oficinadesonido/hanan-cumbia/hananMiniPcb/BD1.kicad_sch

## KiCad design hananMiniPcb/BD1.kicad_sch (2026-06-10)

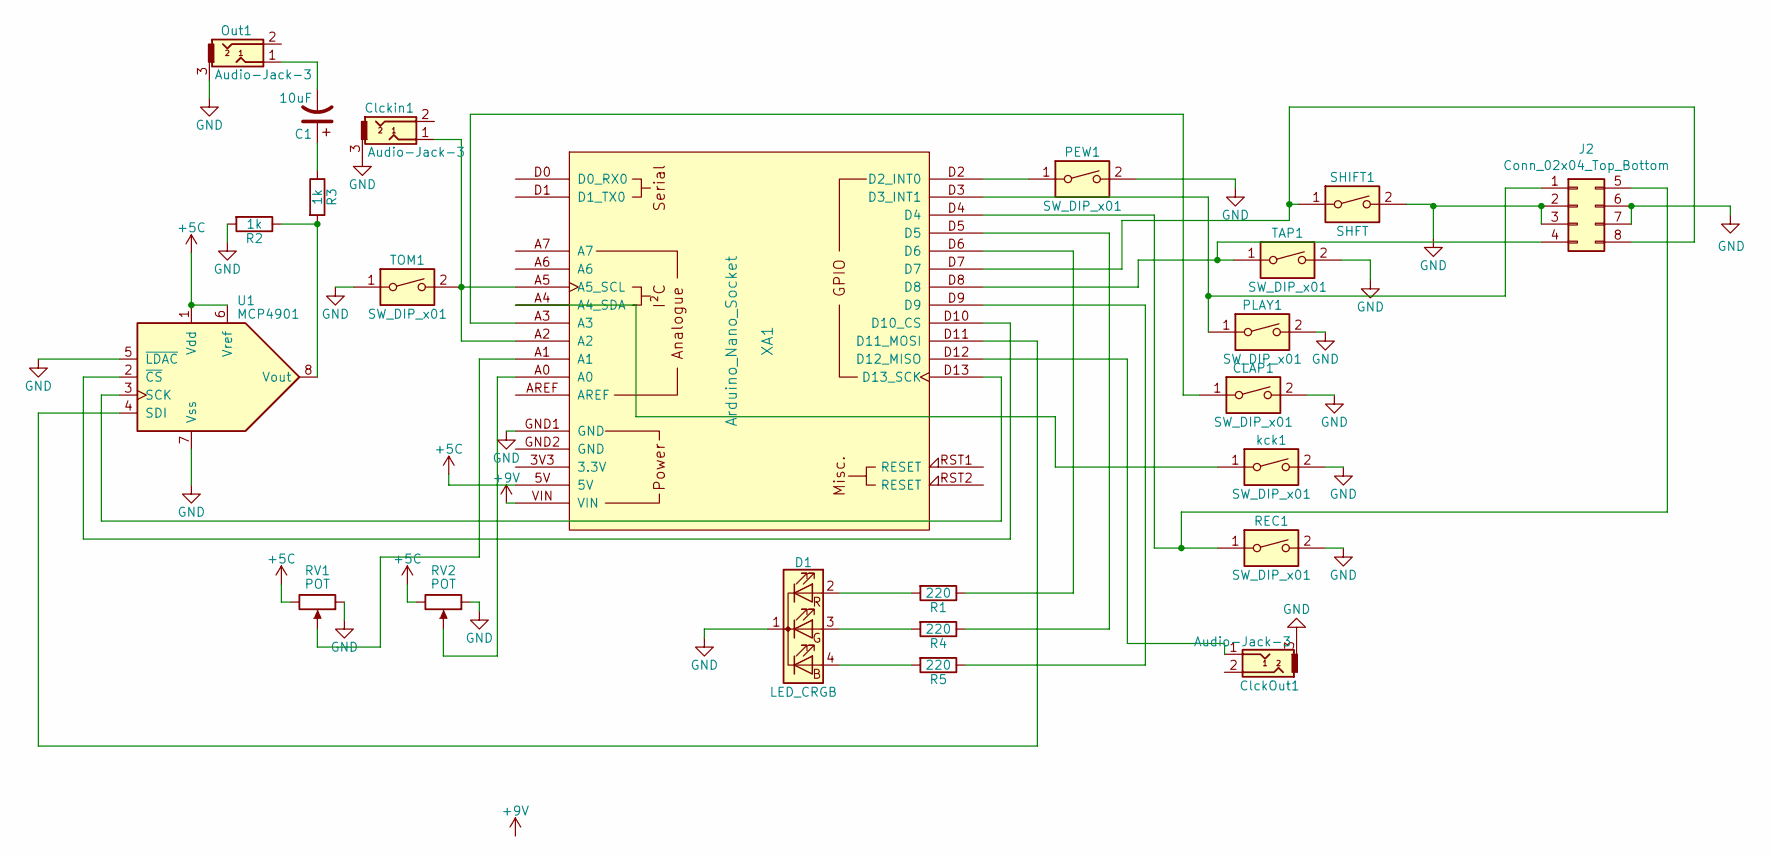
[picture p6: schematic BD1.kicad_sch]

Parts:
C1: 10uF; CP_Radial_D4.0mm_P2.00mm
CLAP1: SW_DIP_x01; SW_PUSH-12mm
ClckOut1: Audio-Jack-3; CONN_Jack_Female_3.5mm_THD
Clckin1: Audio-Jack-3; CONN_Jack_Female_3.5mm_THD
D1: LED_CRGB; LED_RGB_CATCOM_sep
J2: Conn_02x04_Top_Bottom; PinHeader_1x08_P2.00mm_Vertical
Out1: Audio-Jack-3; CONN_Jack_Female_3.5mm_THD
PEW1: SW_DIP_x01; SW_PUSH-12mm
PLAY1: SW_DIP_x01; SW_PUSH_6mm
R1, R4, R5: 220; R_Axial_DIN0207_L6.3mm_D2.5mm_P7.62mm_Horizontal
R2, R3: 1k; R_Axial_DIN0207_L6.3mm_D2.5mm_P7.62mm_Horizontal
REC1: SW_DIP_x01; SW_PUSH_6mm
RV1, RV2: POT; Potentiometer_Alps_RK09K_Single_Vertical
SHIFT1: SHFT; SW_PUSH_6mm
TAP1: SW_DIP_x01; SW_PUSH_6mm
TOM1: SW_DIP_x01; SW_PUSH-12mm
U1: MCP4901; DIP-8_W7.62mm_Socket_LongPads
XA1: Arduino_Nano_Socket
kck1: SW_DIP_x01; SW_PUSH-12mm

Connections:
+5C: RV1.3, RV2.3, U1.1 (Vdd), U1.6 (Vref), XA1.5V
+9V: XA1.VIN
GND: CLAP1.2, ClckOut1.3, Clckin1.3, D1.1 (K), J2.2, J2.3, J2.6, J2.7, Out1.3, PEW1.2, PLAY1.2, R2.2, REC1.2, RV1.1, RV2.1, SHIFT1.2, TAP1.2, TOM1.1, U1.5 (~LDAC), U1.7 (Vss), XA1.GND1 (GND), kck1.2
unnamed: C1.1, R3.1
unnamed: C1.2, Out1.1
unnamed: CLAP1.1, XA1.A3
unnamed: ClckOut1.1, XA1.D12 (D12_MISO)
unnamed: Clckin1.1, TOM1.2, XA1.A2, XA1.A5 (A5_SCL)
unnamed: D1.2 (RA), R1.2
unnamed: D1.3 (GA), R4.2
unnamed: D1.4 (BA), R5.2
unnamed: J2.1, PLAY1.1, XA1.D3 (D3_INT1)
unnamed: J2.4, TAP1.1, XA1.D8
unnamed: J2.5, REC1.1, XA1.D4
unnamed: J2.8, SHIFT1.1, XA1.D7
unnamed: PEW1.1, XA1.D2 (D2_INT0)
unnamed: R1.1, XA1.D6
unnamed: R2.1, R3.2, U1.8 (Vout)
unnamed: R4.1, XA1.D5
unnamed: R5.1, XA1.D9
unnamed: RV1.2, XA1.A1
unnamed: RV2.2, XA1.A0
unnamed: U1.2 (~CS), XA1.D10 (D10_CS)
unnamed: U1.3 (SCK), XA1.D13 (D13_SCK)
unnamed: U1.4 (SDI), XA1.D11 (D11_MOSI)
unnamed: XA1.A4 (A4_SDA), kck1.1
