oficinadesonido/hanan-cumbia/firmware/hanan26Taller/DDS.ino

ISR(TIMER2_COMPA_vect) {
  OCR2A = 50;

  // Reloj de tempo estable: avanza siempre, sin importar la carga de CPU.
  audioclock += AUDIOCLOCK_STEP;


    if (playmode==0){ //reverse
  snare_sample = (pgm_read_byte(&samplebank[snare_off+(indexr)]))-127;
  kick_sample = (pgm_read_byte(&samplebank[kick_off+(index2r)]))-127;
  hat_sample = (pgm_read_byte(&samplebank[hat_off+(index3r)]))-127;
  bass_sample = (((pgm_read_byte(&samplebank[bass_off+(index4r)]))))-127;

  B1_freq_sample = pgm_read_byte(&samplebank[hat_off+(index2vr)])-127;
  B2_freq_sample = (pgm_read_byte(&samplebank[bass_off+(index4vr)]))-127;
    }
    
if (playmode==1){
  snare_sample = (pgm_read_byte(&samplebank[snare_off+(index3)]))-127;
  kick_sample = (pgm_read_byte(&samplebank[kick_off+(index4)]))-127;
  hat_sample = (pgm_read_byte(&samplebank[hat_off+(index)]))-127;
  bass_sample = (((pgm_read_byte(&samplebank[bass_off+(index2)]))))-127;
  
  noise_sample = (((pgm_read_byte(&noise_table[(index5)]))))-127;

  B1_freq_sample = pgm_read_byte(&samplebank[hat_off+(index_freq_1)])-127;
  B2_freq_sample = (pgm_read_byte(&samplebank[bass_off+(index_freq_2)]))-127;
}
sample_sum=snare_sample+kick_sample+hat_sample+bass_sample+B1_freq_sample+B2_freq_sample;

if (noise_mode==1){

sample_holder1= (sample_sum^(noise_sample>>1))+127;


if (B1_latch ==0 && B2_latch==0  && B3_latch==0  && B4_latch==0 ){
 sample=127 ;
  }
  else{
sample=sample_holder1;
  }
  
}

if (noise_mode==0){
  sample= ((snare_sample+kick_sample+hat_sample+bass_sample+B1_freq_sample+B2_freq_sample))+127;

}
  byte sample_out=constrain(sample,0,255);


   dac.output(sample_out);

  ///////////////////////////////////////////////////////////////////////////////

  if (playmode==0){
    // length-1: con indice forward en 0 (idle), length a secas leeria [length],
    // fuera del sample (en el bass = fuera del banco -> DC de -127 en reverse).
    indexr=(index3-(snare_length-1))*-1;
    index2r=(index4-(kick_length-1))*-1;
    index3r=(index-(tick_length-1))*-1;
    index4r=(index2-(bass_length-1))*-1;
    index2vr=(index_freq_1-(tick_length-1))*-1;
    index4vr=(index_freq_2-(bass_length-1))*-1;

  }
  
  if (B1_latch==1){
    accumulator += pot1;
    index=(accumulator >> (6));  
    // >= : el indice length ya esta FUERA del sample. En el banco unico, leer
    // [length] del ultimo sample (bass) cae fuera del array -> byte basura (0)
    // -> pico de -127 = clic al final del sonido.
    if (index>=tick_length){

      index=0;
      accumulator=0;
      B1_latch=0;
    }
  }

  if (B2_latch==1){
    accumulator2 += (pot2);
    index2=(accumulator2 >> (6));  
    if (index2>=bass_length){

      index2=0;
      accumulator2=0;
      B2_latch=0;
    }
  }

  if (B3_latch==1){
    accumulator3 += (128);
    index3=(accumulator3 >> 6);  
    if (index3>=snare_length){

      index3=0;
      accumulator3=0;
      B3_latch=0;
    }
  }

  if (B4_latch==1){
    accumulator4 += (157);
   // index4b=(accumulator4 >> (6));  
    index4=(accumulator4 >> (6));
    if (index4>=kick_length){

      index4=0;
      accumulator4=0;
      B4_latch=0;
    }
  }

  accu_freq_1 += kf;
  index_freq_1=(accu_freq_1 >> (6));  
  if (B1_seq_trigger==1){
    kf=B1_freq_sequence[loopstepf+banko];
    kfe=kf;
  }

  if (index_freq_1>=tick_length){
    kf=0;
    index_freq_1=0;
    accu_freq_1=0;
    B1_seq_latch=0;
  }


  accu_freq_2 += pf;
  index_freq_2=(accu_freq_2 >> (6));

  if (B2_seq_trigger==1){
    pf=B2_freq_sequence[loopstepf+banko];
  }
  if (index_freq_2>=bass_length){
    pf=0;
    index_freq_2=0;
    accu_freq_2=0;
    B2_seq_latch=0;
  }
  

  if (noise_mode==1){
    accumulator5 += (pot3);
   // index4b=(accumulator4 >> (6));  
    index5=(accumulator5 >> (6));
    if (index5>pot4){
      index5=0;
      accumulator5=0;
    }
  }
}
